JordanAceto/micro_ox/jack_panel/docs/2D/jack_panel_B.Cu.pdf

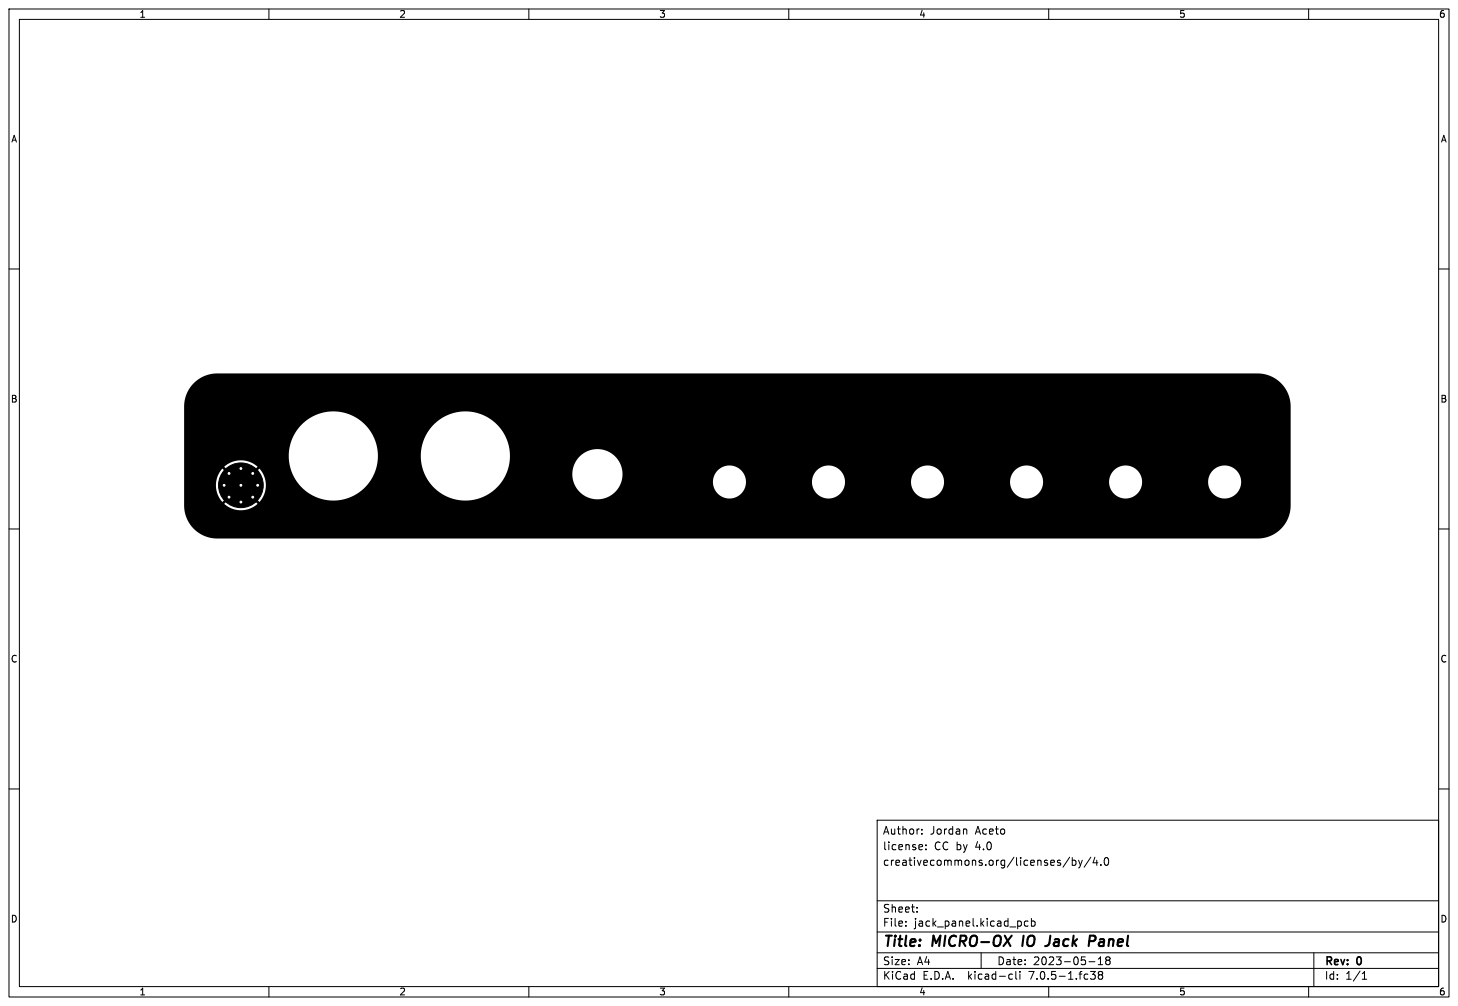
[picture p47: page 1]

Id: 1/1 Title: MICRO-OX IO Jack Panel File: jack_panel.kicad_pcb Sheet: creativecommons.org/licenses/by/4.0
