JordanAceto/micro_ox/circuit_boards/modulation_board/docs/2D/modulation_board_B.Cu.pdf

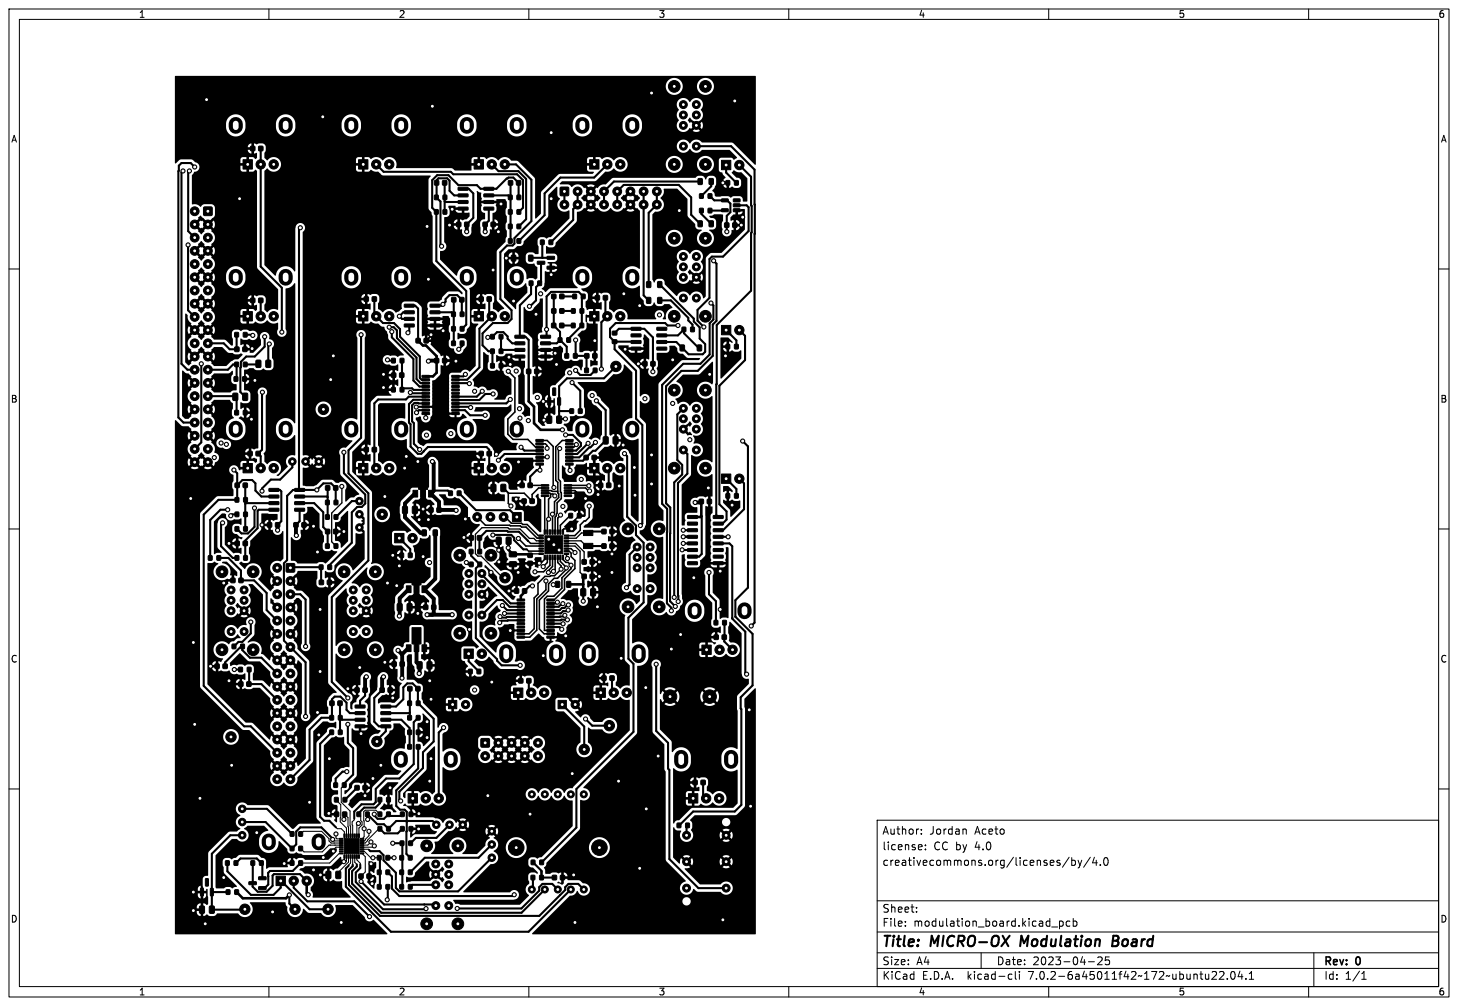
[picture p49: page 1]

File: modulation_board.kicad_pcb Sheet: creativecommons.org/licenses/by/4.0

Id: 1/1 Title: MICRO-OX Modulation Board
