JordanAceto/micro_ox/circuit_boards/modulation_board/docs/2D/modulation_board_B.SilkS.pdf

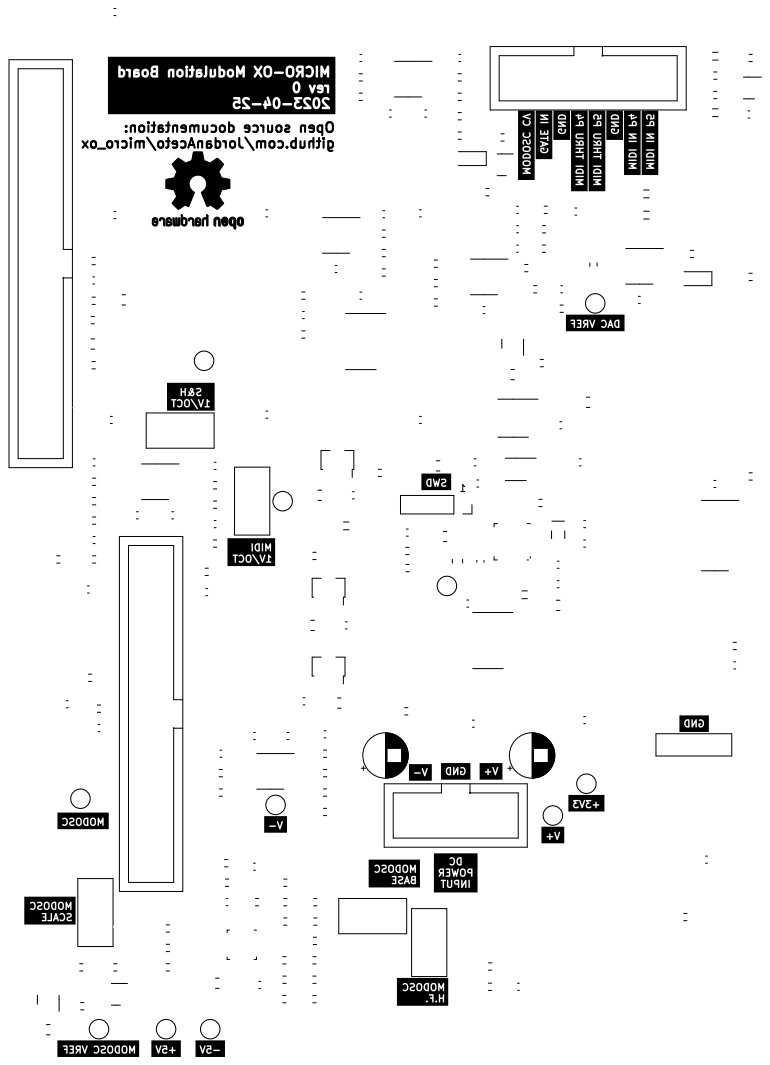
[picture p50: page 1]

Open source documentation: github.com/JordanAceto/micro_ox

File: modulation_board.kicad_pcb Sheet: creativecommons.org/licenses/by/4.0

Id: 1/1 Title: MICRO-OX Modulation Board
