JordanAceto/micro_ox/circuit_boards/power_supply_and_io_board/docs/2D/power_supply_and_io_board_F.SilkS.pdf

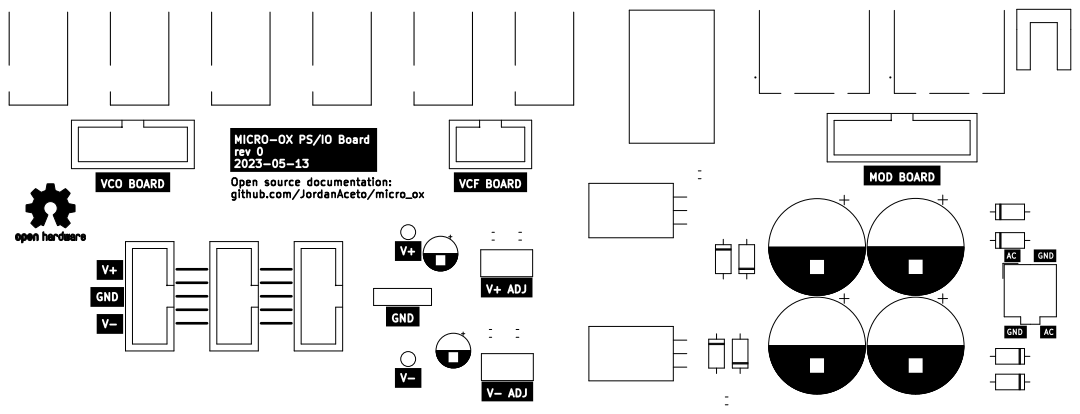
[picture p58: page 1]

Id: 1/1 Title: MICRO-OX Modulation Board
