JordanAceto/micro_ox/circuit_boards/VCF_VCA_board/docs/2D/VCF_VCA_board_B.Cu.pdf

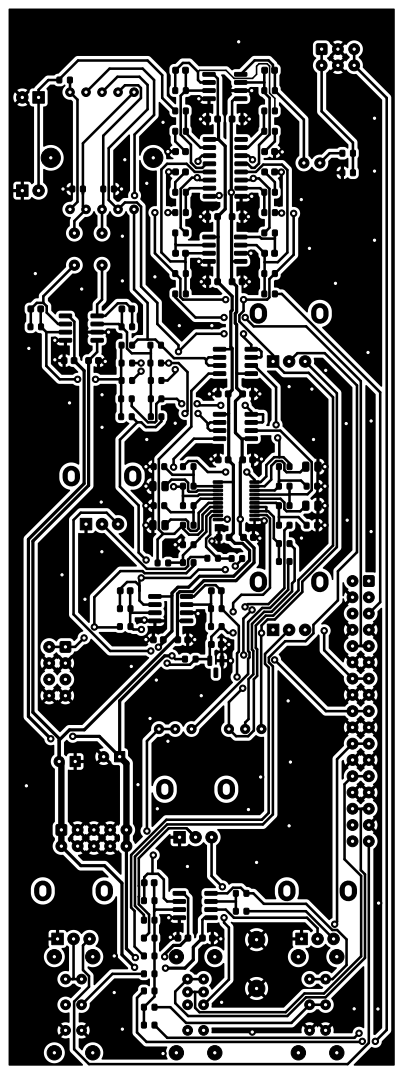
[picture p60: page 1]

File: VCF_VCA_board.kicad_pcb Sheet: creativecommons.org/licenses/by/4.0

Id: 1/1 Title: MICRO-OX VCF/VCA board
