JordanAceto/micro_ox/front_panel/docs/2D/micro_ox_front_panel_F.SilkS.pdf

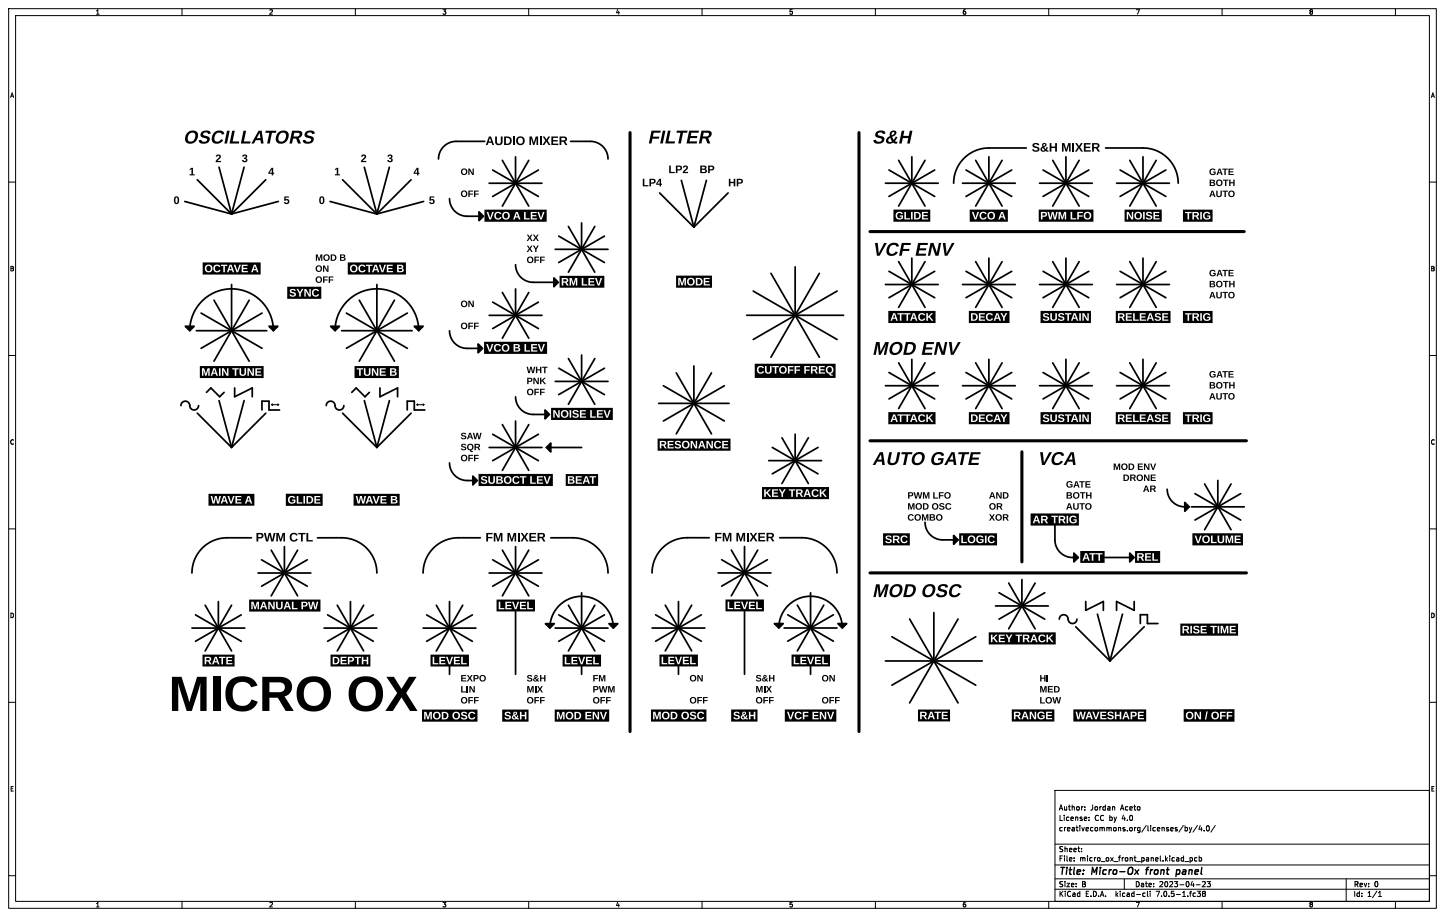
[picture p69: page 1]
